dimitris-lagos/j1850pwm-stn1110/global.h

#ifndef __global_h_included__
#define __global_h_included__

#define WELLCOME_TEXT "Jiml OBD2"
#define CONSUMPTION_PERCENT_DEVIATION 17
#define DEVIATION_FACTOR (((float)CONSUMPTION_PERCENT_DEVIATION / 100.00) + 1.00)
#define MEDIAN_MILAGE 7.3000


#endif
